Atif-Mahmud/8Bot/eagle/Motherboard 8bot negative no margin.png

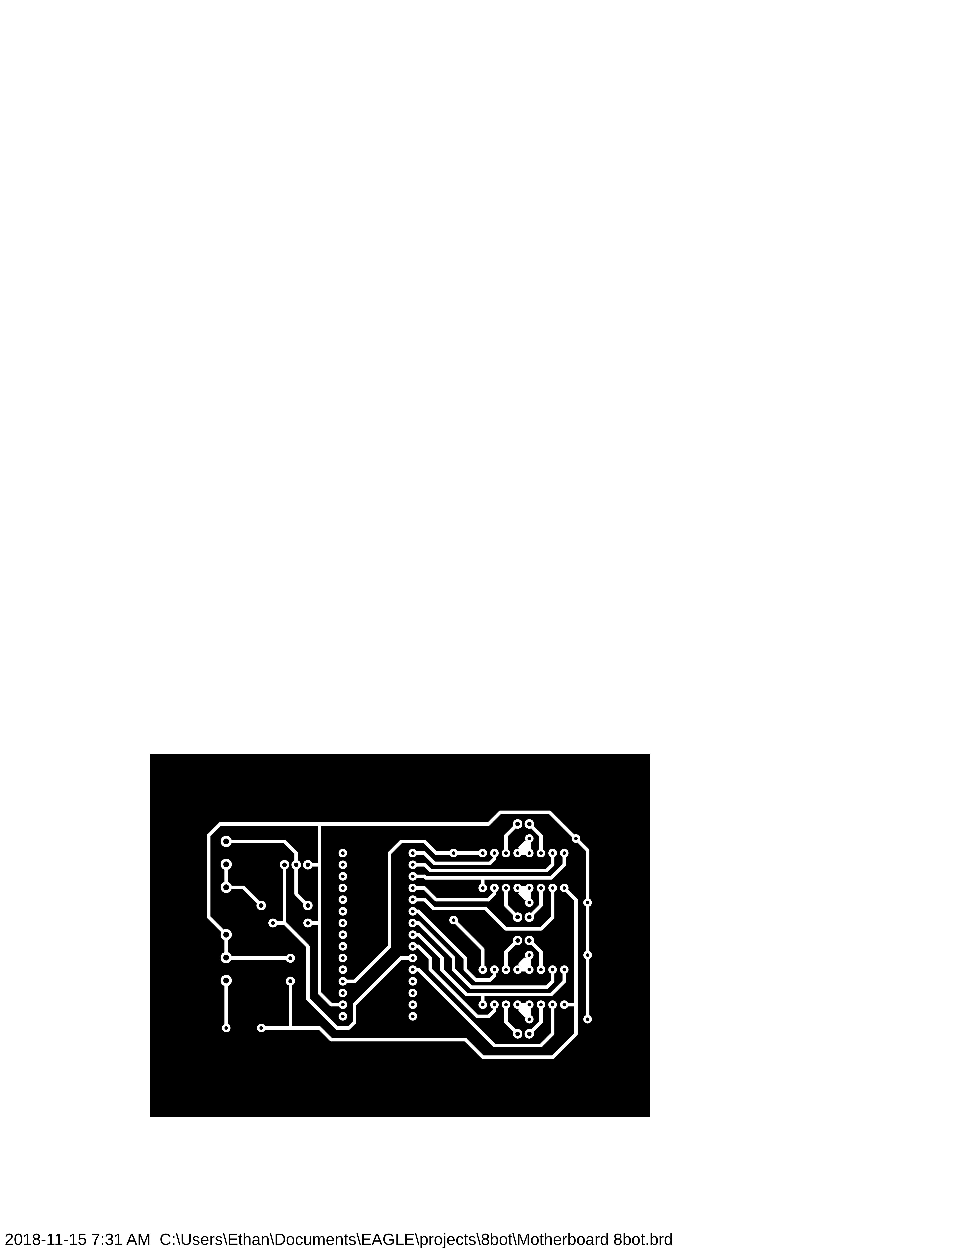
eagle/Motherboard 8bot negative no margin.png
